marcgarrofe/LuciRobot/3d/9v.png

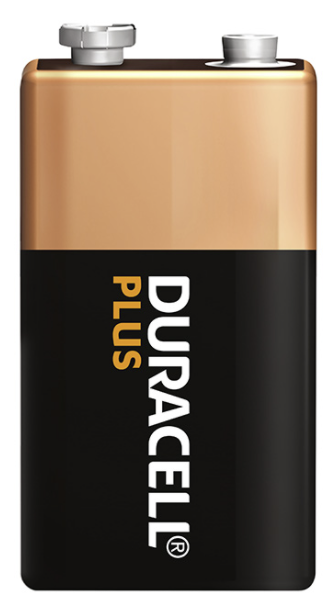
3d/9v.png
