marcgarrofe/LuciRobot/3d/51XoWRcYl9L._AC_SL1200_.jpg

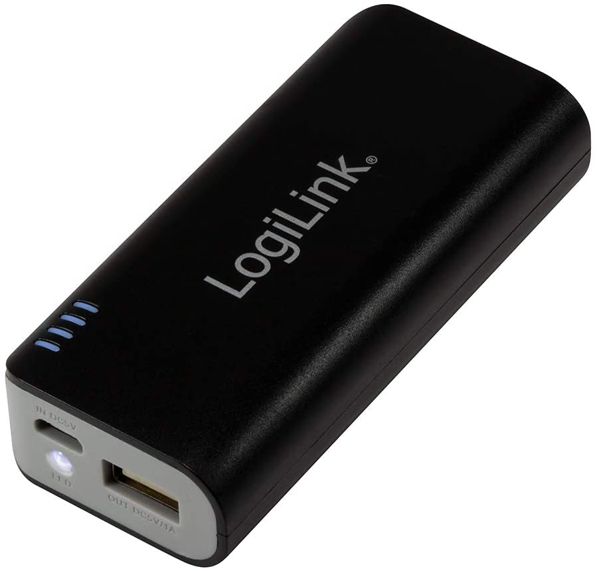
3d/51XoWRcYl9L._AC_SL1200_.jpg
