marcgarrofe/LuciRobot/3d/81jHWSkxcjL._SL1500_.jpg

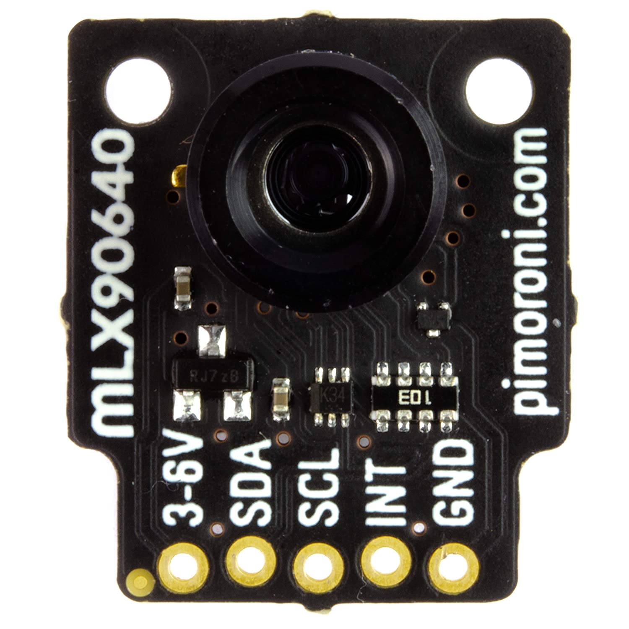
3d/81jHWSkxcjL._SL1500_.jpg
