marcgarrofe/LuciRobot/3d/2022-03-27 12_29_53-Power Bank 5000 logilink - Búsqueda de Google y 8 páginas más - Personal_ Micros.png

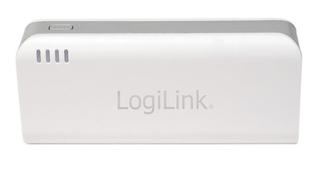
3d/2022-03-27 12_29_53-Power Bank 5000 logilink - Búsqueda de Google y 8 páginas más - Personal_ Micros.png
