marcgarrofe/LuciRobot/3d/Arduino-UNO-frontal.jpg

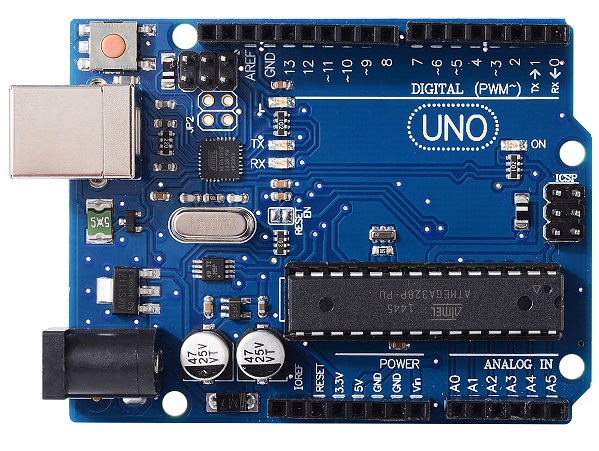
3d/Arduino-UNO-frontal.jpg
