marcgarrofe/LuciRobot/3d/disenybasic.jpg

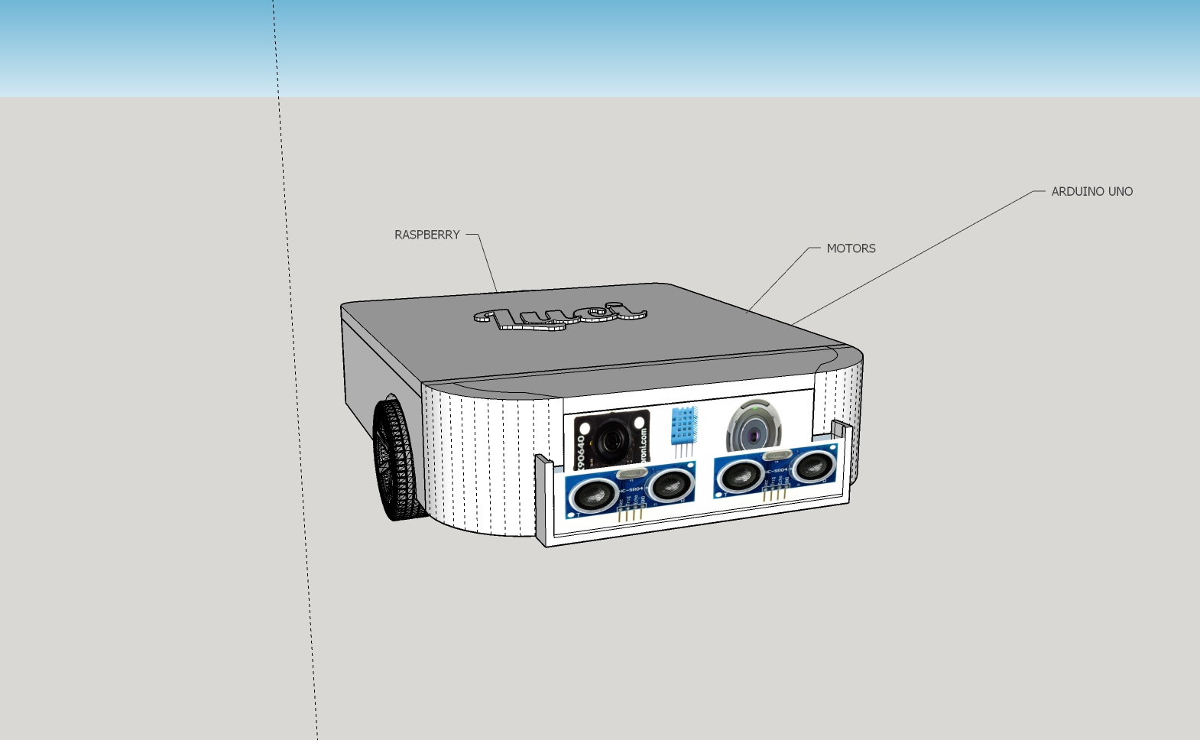
3d/disenybasic.jpg
