marcgarrofe/LuciRobot/3d/hc-sr04.jpg

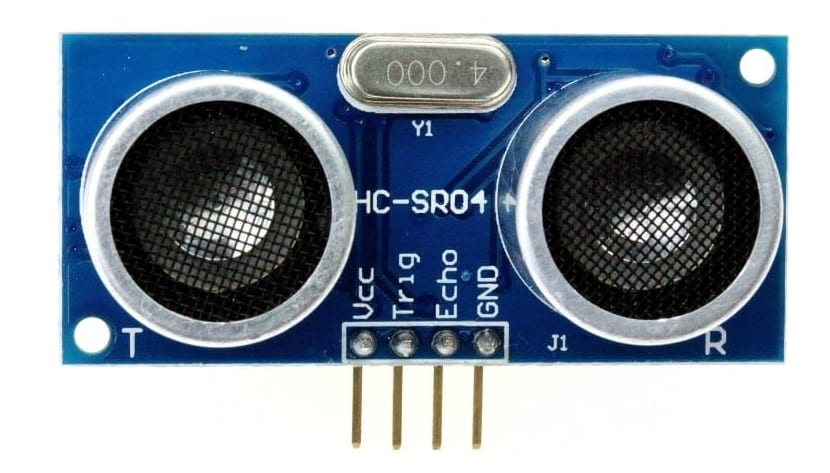
3d/hc-sr04.jpg
