marcgarrofe/LuciRobot/3d/modul-ultrasons-temperatura.png

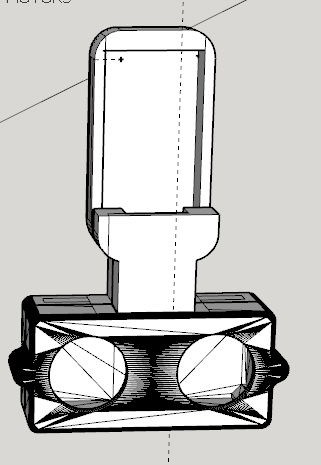
3d/modul-ultrasons-temperatura.png
