marcgarrofe/LuciRobot/3d/raspberry-pi-4-model-b.jpg

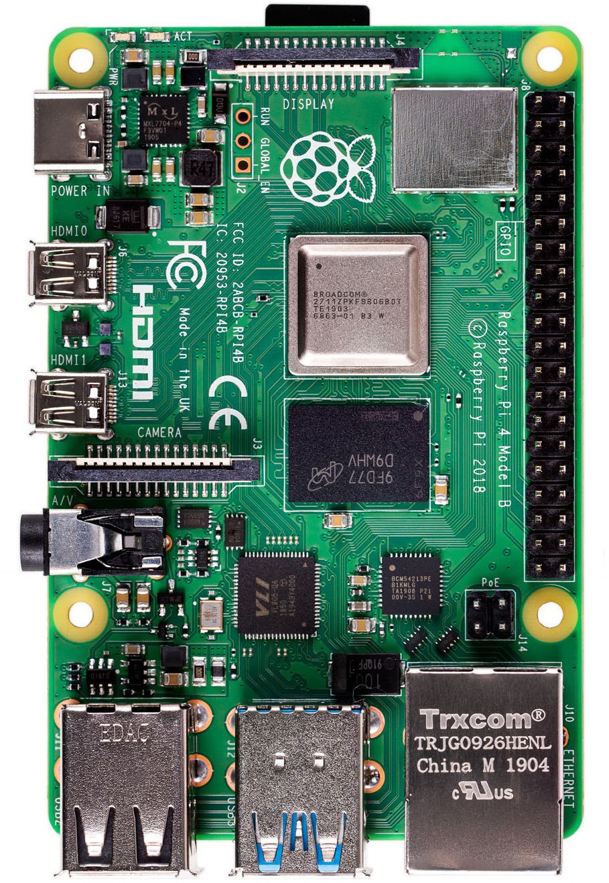
3d/raspberry-pi-4-model-b.jpg
