marcgarrofe/LuciRobot/3d/Sensor-DHT11-Humeda-SDTH0011-imagen-1-e1632512321455.jpg

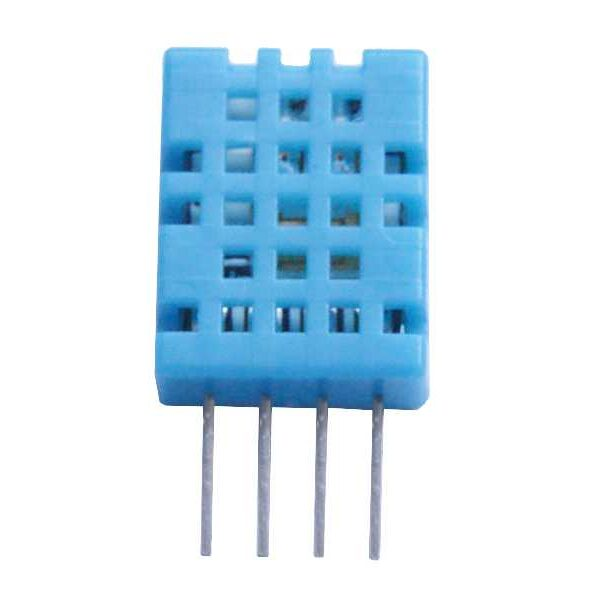
3d/Sensor-DHT11-Humeda-SDTH0011-imagen-1-e1632512321455.jpg
