marcgarrofe/LuciRobot/3d/webcam_noun_001_19086.jpg

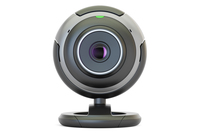
3d/webcam_noun_001_19086.jpg
