marcgarrofe/LuciRobot/sprints/sprint7/sensors.jpeg

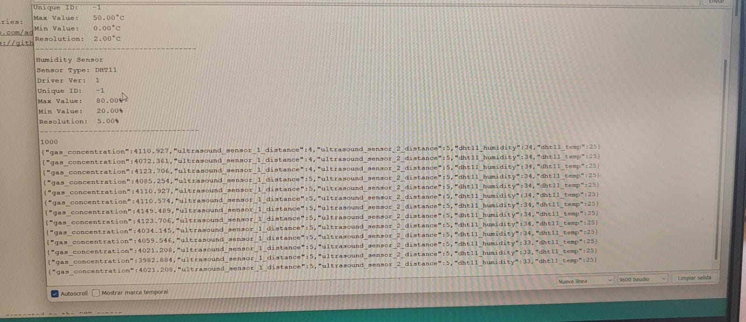
sprints/sprint7/sensors.jpeg
